rusaakkmods/microboy_midi/schematics/megaboy_midi/megaboy_midi.kicad_pcb

## KiCad design modulogue_vco.kicad_sch

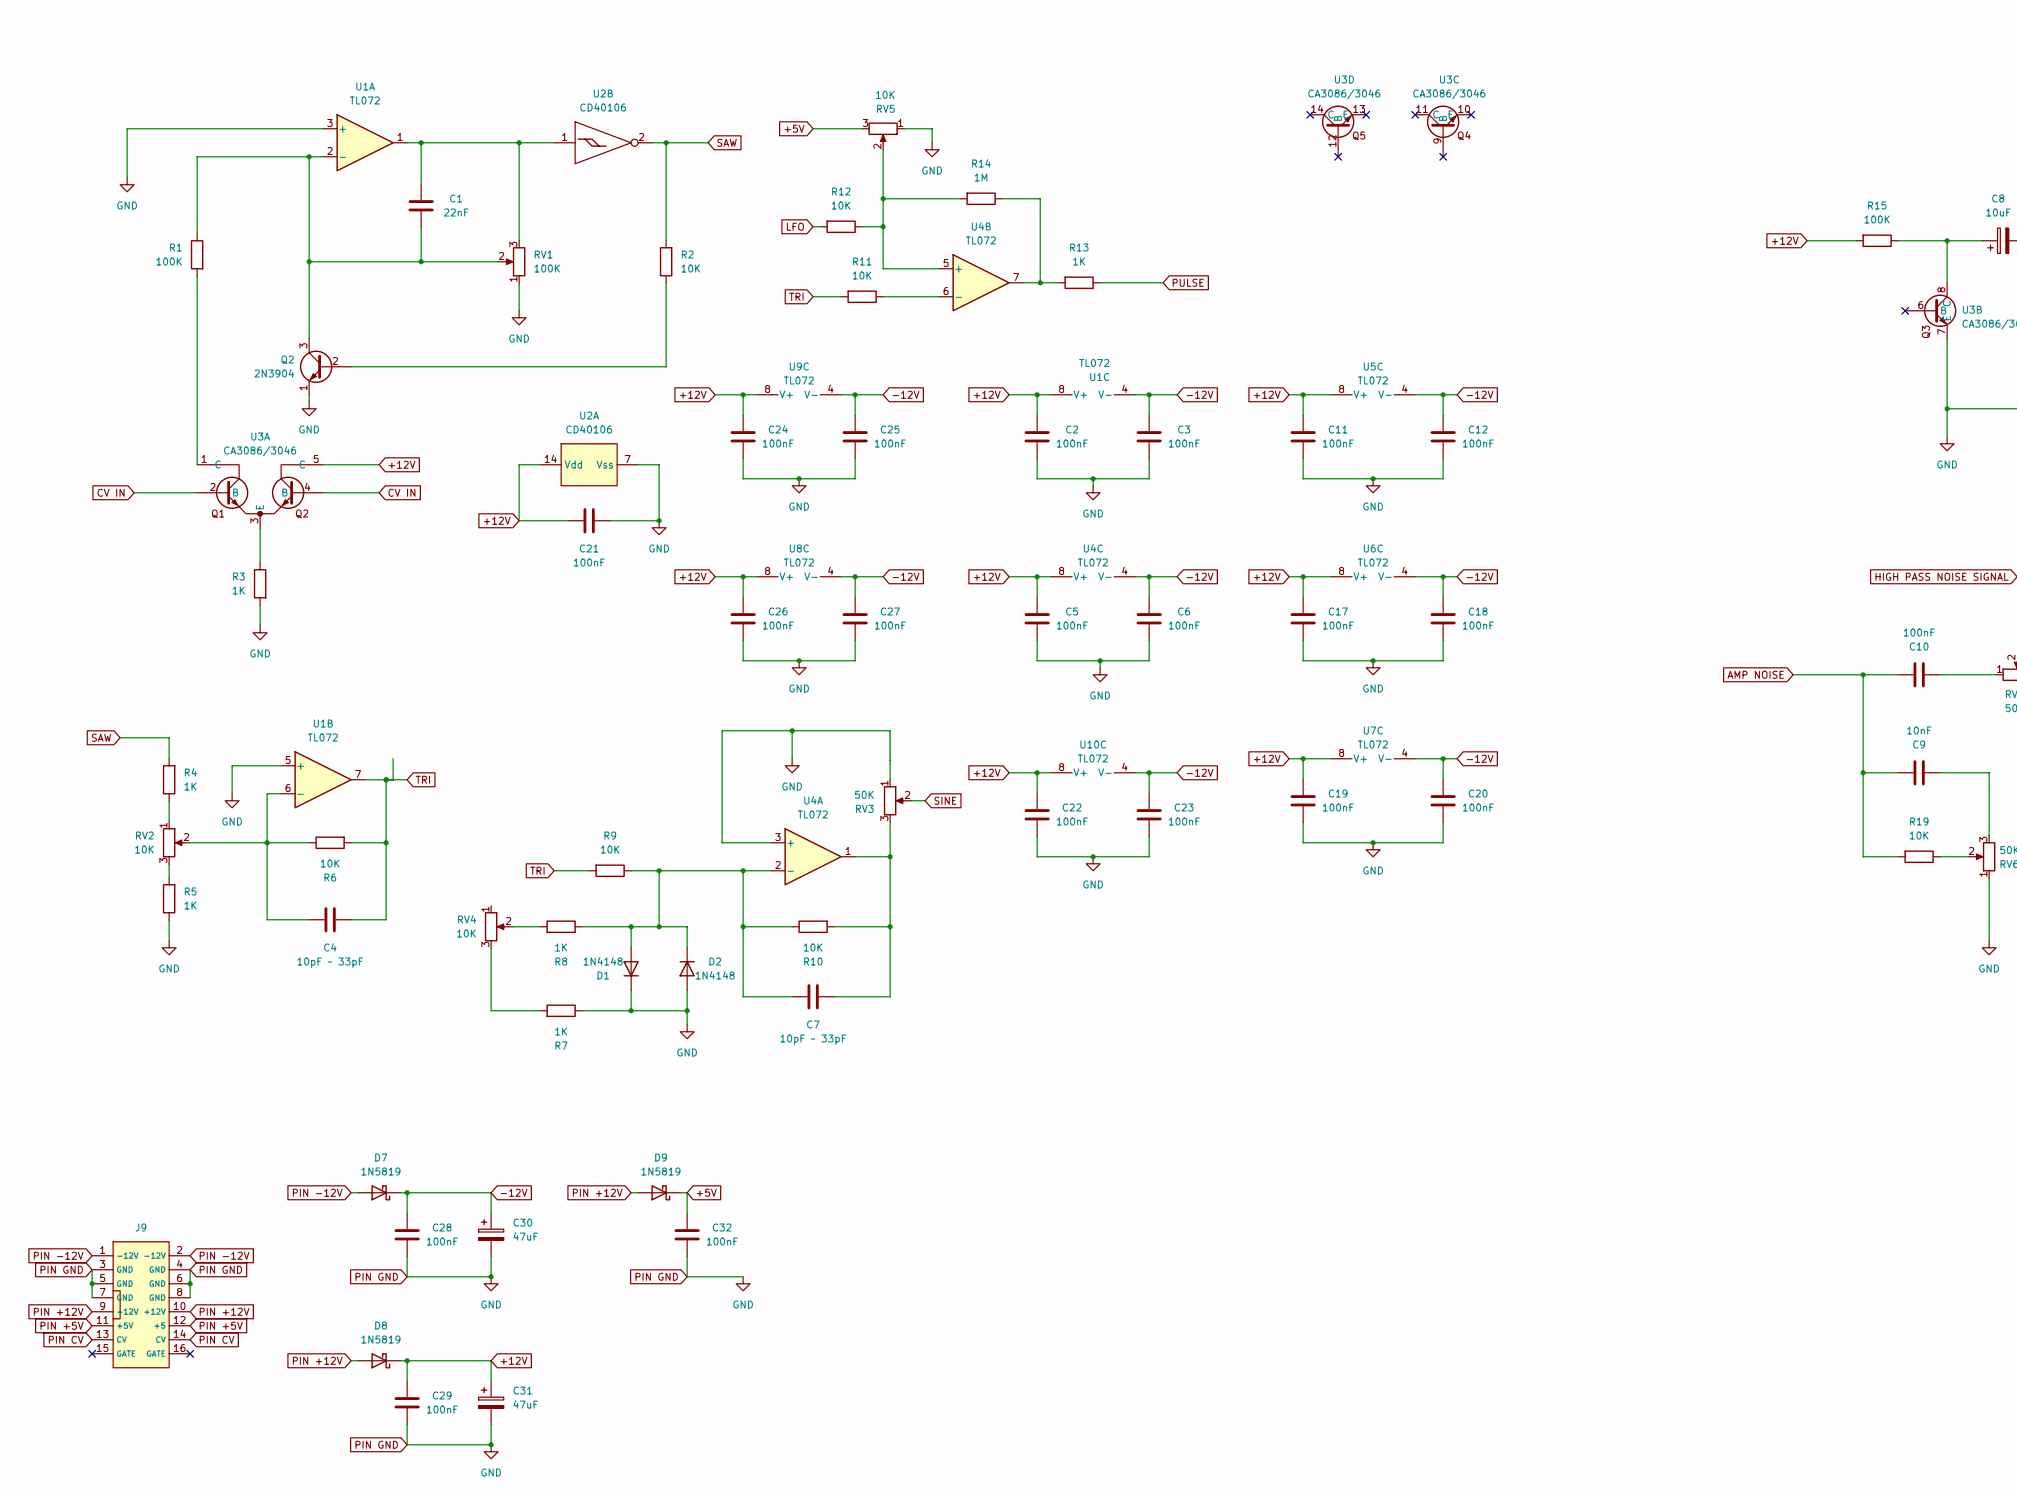
[picture p2: schematic modulogue_vco.kicad_sch, part in row 1, column 1]

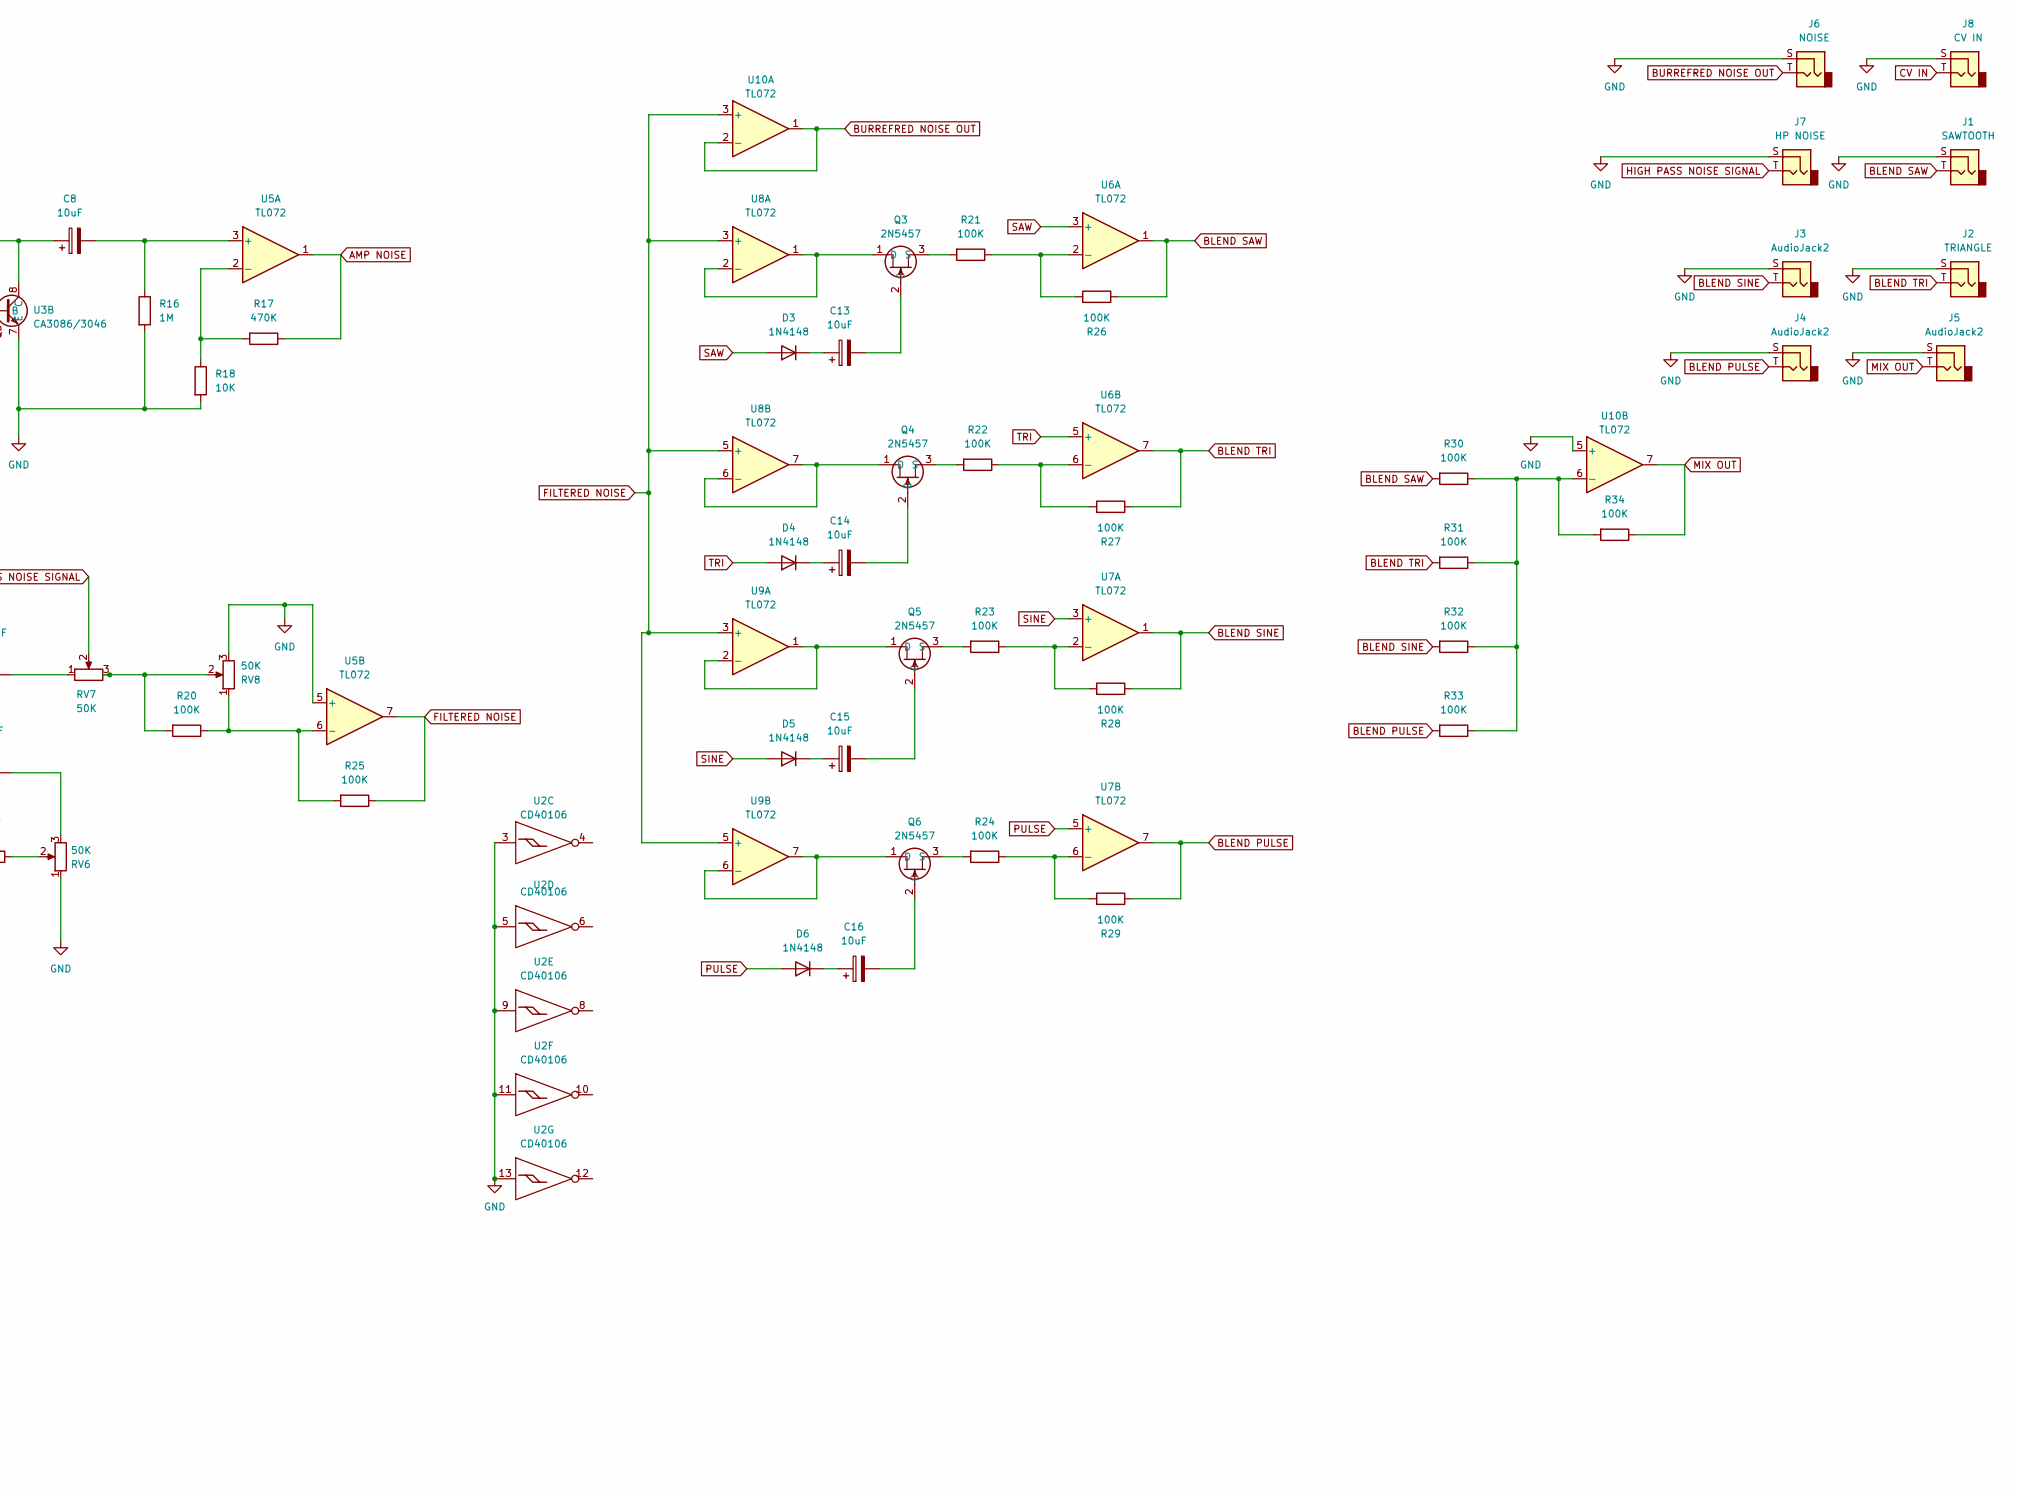
[picture p3: schematic modulogue_vco.kicad_sch, part in row 1, column 2]

Parts:
C1: 22nF
C2, C3, C5, C6, C10, C11, C12, C17, C18, C19, C20, C21, C22, C23, C24, C25, C26, C27, C28, C29, C32: 100nF
C4, C7: 10pF ~ 33pF
C8, C13, C14, C15, C16: 10uF
C9: 10nF
C30, C31: 47uF
D1, D2: 1N4148
D3, D4, D5, D6: 1N4148; D_DO-35_SOD27_P7.62mm_Horizontal
D7, D8, D9: 1N5819; D_DO-41_SOD81_P10.16mm_Horizontal
J1: SAWTOOTH
J2: TRIANGLE
J3, J4, J5: AudioJack2
J6: NOISE
J7: HP NOISE
J8: CV IN
J9: IDC-Header_2x08_P2.54mm_Vertical
Q2: 2N3904; TO-92_Inline
Q3, Q4, Q5, Q6: 2N5457
R1, R15, R20, R21, R22, R23, R24, R25, R26, R27, R28, R29, R30, R31, R32, R33, R34: 100K
R2, R6, R9, R10, R11, R12, R18, R19: 10K
R3, R4, R5, R7, R8, R13: 1K
R14, R16: 1M
R17: 470K
RV1: 100K
RV2, RV4, RV5: 10K
RV3, RV6, RV7, RV8: 50K
U1, U4, U5, U6, U7, U8, U9, U10: TL072
U2: CD40106; DIP-14_W7.62mm_Socket
U3: CA3086/3046

Connections:
+5V: C32.2, D9.1 (K), RV5.3
+12V: C2.2, C5.2, C11.2, C17.2, C19.2, C21.1, C22.2, C24.2, C26.2, C29.2, C31.1, D8.1 (K), R15.2, U1.8 (V+), U2.14 (Vdd), U3.5 (C), U4.8 (V+), U5.8 (V+), U6.8 (V+), U7.8 (V+), U8.8 (V+), U9.8 (V+), U10.8 (V+)
-12V: C3.2, C6.2, C12.2, C18.2, C20.2, C23.2, C25.2, C27.2, C28.2, C30.1, D7.1 (K), U1.4 (V-), U4.4 (V-), U5.4 (V-), U6.4 (V-), U7.4 (V-), U8.4 (V-), U9.4 (V-), U10.4 (V-)
AMP NOISE: C9.2, C10.2, R17.1, R19.2, U5.1
BLEND PULSE: J4.T, R29.1, R33.2, U7.7
BLEND SAW: J1.T, R26.1, R30.2, U6.1
BLEND SINE: J3.T, R28.1, R32.2, U7.1
BLEND TRI: J2.T, R27.1, R31.2, U6.7
BURREFRED NOISE OUT: J6.T, U10.1, U10.2 (-)
CV IN: J8.T, U3.2 (B), U3.4 (B)
FILTERED NOISE: R25.1, U5.7, U8.3 (+), U8.5 (+), U9.3 (+), U9.5 (+), U10.3 (+)
GND: C2.1, C3.1, C5.1, C6.1, C11.1, C12.1, C17.1, C18.1, C19.1, C20.1, C21.2, C22.1, C23.1, C24.1, C25.1, C26.1, C27.1, C28.1, C29.1, C30.2, C31.2, C32.1, D1.1 (K), D2.2 (A), J1.S, J2.S, J3.S, J4.S, J5.S, J6.S, J7.S, J8.S, J9.3 (GND), J9.4 (GND), J9.5 (GND), J9.6 (GND), J9.7 (GND), J9.8 (GND), Q2.1 (E), R3.2, R5.1, R7.1, R16.2, R18.2, RV1.1, RV3.1, RV5.1, RV6.1, RV8.3, U1.3 (+), U1.5 (+), U2.3, U2.5, U2.7 (Vss), U2.9, U2.11, U2.13, U3.7 (E), U4.3 (+), U5.5 (+), U10.5 (+)
HIGH PASS NOISE SIGNAL: J7.T, RV7.2
LFO: R12.2
MIX OUT: J5.T, R34.1, U10.7
unnamed: C1.1, Q2.3 (C), R1.1, RV1.2, U1.2 (-)
unnamed: C1.2, RV1.3, U1.1, U2.1
unnamed: C4.1, R6.1, RV2.2, U1.6 (-)
unnamed: C7.1, D1.2 (A), D2.1 (K), R8.1, R9.1, R10.1, U4.2 (-)
unnamed: C7.2, R10.2, RV3.3, U4.1
unnamed: C8.1, R15.1, U3.8 (C)
unnamed: C8.2, R16.1, U5.3 (+)
unnamed: C9.1, RV6.3
unnamed: C10.1, RV7.1
unnamed: C13.1, D3.1 (K)
unnamed: C13.2, Q3.2 (G)
unnamed: C14.1, D4.1 (K)
unnamed: C14.2, Q4.2 (G)
unnamed: C15.1, D5.1 (K)
unnamed: C15.2, Q5.2 (G)
unnamed: C16.1, D6.1 (K)
unnamed: C16.2, Q6.2 (G)
unnamed: Q2.2 (B), R2.1
unnamed: Q3.1 (D), U8.1, U8.2 (-)
unnamed: Q3.3 (S), R21.2
unnamed: Q4.1 (D), U8.6 (-), U8.7
unnamed: Q4.3 (S), R22.2
unnamed: Q5.1 (D), U9.1, U9.2 (-)
unnamed: Q5.3 (S), R23.2
unnamed: Q6.1 (D), U9.6 (-), U9.7
unnamed: Q6.3 (S), R24.2
unnamed: R1.2, U3.1 (C)
unnamed: R3.1, U3.3 (E)
unnamed: R4.1, RV2.1
unnamed: R5.2, RV2.3
unnamed: R7.2, RV4.3
unnamed: R8.2, RV4.2
unnamed: R11.1, U4.6 (-)
unnamed: R12.1, R14.2, RV5.2, U4.5 (+)
unnamed: R13.2, R14.1, U4.7
unnamed: R17.2, R18.1, U5.2 (-)
unnamed: R19.1, RV6.2
unnamed: R20.1, R25.2, RV8.1, U5.6 (-)
unnamed: R20.2, RV7.3, RV8.2
unnamed: R21.1, R26.2, U6.2 (-)
unnamed: R22.1, R27.2, U6.6 (-)
unnamed: R23.1, R28.2, U7.2 (-)
unnamed: R24.1, R29.2, U7.6 (-)
unnamed: R30.1, R31.1, R32.1, R33.1, R34.2, U10.6 (-)
PIN +5V: J9.11 (+5V), J9.12 (+5)
PIN +12V: D8.2 (A), D9.2 (A), J9.9 (+12V), J9.10 (+12V)
PIN -12V: D7.2 (A), J9.1 (-12V), J9.2 (-12V)
PIN CV: J9.13 (CV), J9.14 (CV)
PULSE: D6.2 (A), R13.1, U7.5 (+)
SAW: D3.2 (A), R2.2, R4.2, U2.2, U6.3 (+)
SINE: D5.2 (A), RV3.2, U7.3 (+)
TRI: C4.2, D4.2 (A), R6.2, R9.2, R11.2, U1.7, U6.5 (+)
