rusaakkmods/microboy_midi/include/build.h

#pragma once

#define _USB_PRODUCT "microBOY"
#define _PRODUCT_LINE "LSDJ - mi.out"
#define _USB_MANUFACTURER "rusaakkmods"
#define _VERSION "v1.0.0"
#define _YEAR "2025"
#define _GITHUB "https://t.ly/e2qlD"
#define _AUTHOR "pria jatnika"

// #define DEBUG_MODE /* enable debug mode */
// #define USE_MIDI_h               /* use MIDI Library for MIDI Serial Communication (faster but unstable! buffer overflow in faster rate) */
// #define ARDUINOBOY_READER        /* use Arduinoboy version of reader also stable, tweak byteDelay for better stability */
 #define NON_BLOCKING_DELAY /* use non-blocking read for Gameboy Serial Communication (more stable when enable clock) */
